Dustin21/interrogator-hardware/contract/io_map.md

# IO map — generated from the pinned USR snapshot

Contract pin: `881fbc1ba3e9c62c94d481077ae7dd061a07874b` · sensors: 16 · electrical facets still pending sign-off (USR-3): **16**

> Generated file — do not edit. Regenerate with `python3 contract/scripts/ingest.py`.

| sensor_type | part | vendor | wire_token | class | bus | i2c addrs | logic V | elec status | datasheet rev |
|---|---|---|---|---|---|---|---|---|---|
| ADS1115 | ADS1115 | Texas Instruments | ADS1115 | adc | i2c | — | 3.3 | ⚠ pending | TODO |
| AMG8833 | AMG8833 (Grid-EYE) | Panasonic | AMG8833 | thermal_imager | i2c | — | 3.3 | ⚠ pending | TODO |
| AS7263 | AS7263 | ams OSRAM | AS7263 | spectral_nir | i2c | — | 3.3 | ⚠ pending | TODO |
| AS7331 | AS7331 | ams OSRAM | AS7331 | uv | i2c | — | 3.3 | ⚠ pending | TODO |
| AS7343 | AS7343 | ams OSRAM | AS7343 | spectral_vis | i2c | — | 3.3 | ⚠ pending | TODO |
| BME688 | BME688 | Bosch Sensortec | BME688 | env_gas | i2c | — | 3.3 | ⚠ pending | BST-BME688-DS000-03 Rev 1 |
| BMV080 | BMV080 | Bosch Sensortec | BMV080 | particulate | i2c | — | 3.3 | ⚠ pending | TODO |
| BNO085 | BNO085 | Bosch Sensortec (CEVA/Hillcrest) | BNO085 | imu | i2c | — | 3.3 | ⚠ pending | TODO |
| MAX30102 | MAX30102 | Maxim Integrated (ADI) | MAX30102 | pulse_oximeter | i2c | — | 3.3 | ⚠ pending | TODO |
| MIKROE_4036 | MIKROE-4036 | MikroElektronika | MIKROE_4036 | radiation | digital_pulse | — | 3.3 | ⚠ pending | TODO |
| MPR121 | MPR121 | NXP Semiconductors | MPR121 | capacitive_touch | i2c | — | 3.3 | ⚠ pending | TODO |
| NEO_M9N | NEO-M9N | u-blox | GPS | gnss | i2c | — | 3.3 | ⚠ pending | TODO |
| SGP41 | SGP41 | Sensirion | SGP41 | voc_nox_gas | i2c | — | 3.3 | ⚠ pending | TODO |
| TMAG5273 | TMAG5273 | Texas Instruments | TMAG5273 | magnetometer | i2c | — | 3.3 | ⚠ pending | TODO |
| VL53L8CX | VL53L8CX | STMicroelectronics | VL53L8CX | tof_imager | i2c | — | 3.3 | ⚠ pending | TODO |
| XM125 | XM125 (A121) | Acconeer | XM125 | radar_presence | i2c | — | 3.3 | ⚠ pending | TODO |
