Dustin21/interrogator-hardware/enclosure/bean_iso.png

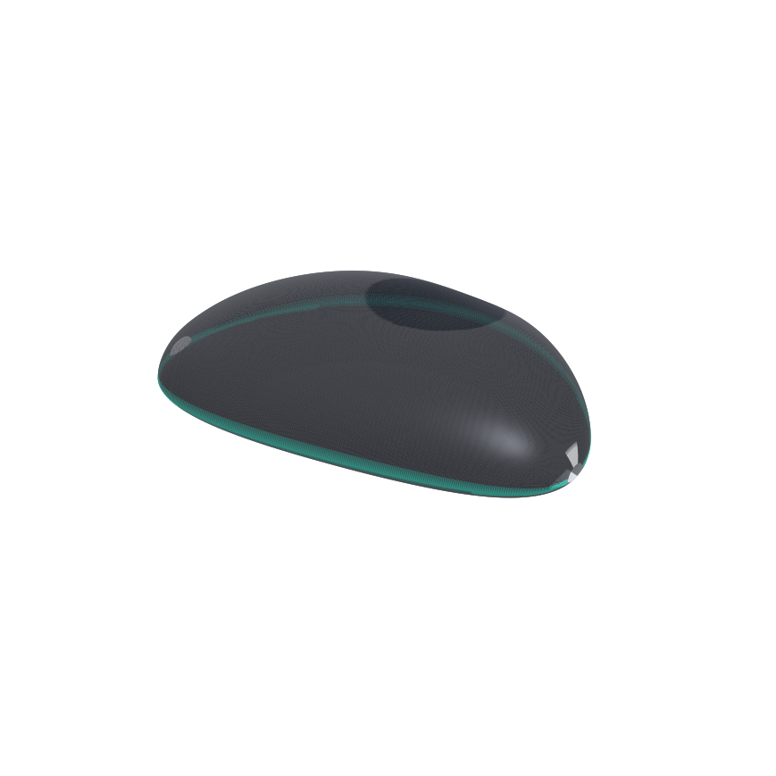
enclosure/bean_iso.png
