Dustin21/interrogator-hardware/enclosure/bean_side.png

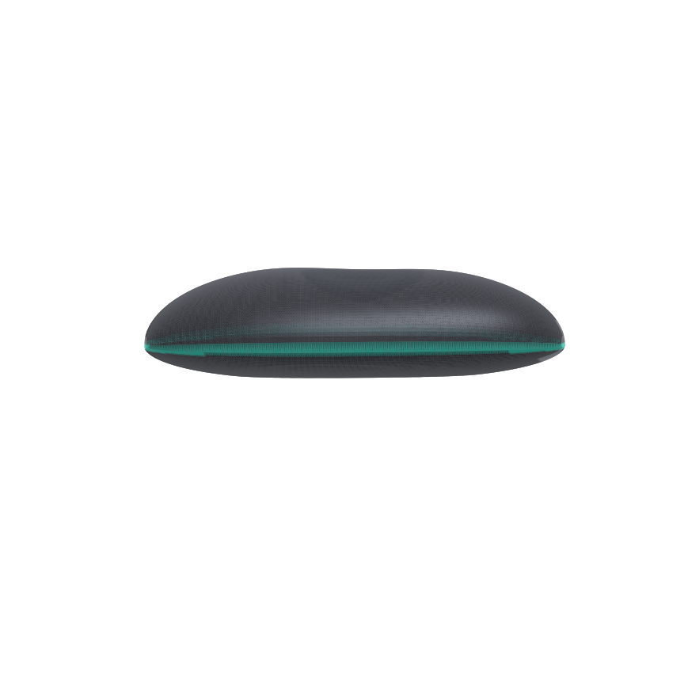
enclosure/bean_side.png
