Dustin21/interrogator-hardware/enclosure/bean_thumb.png

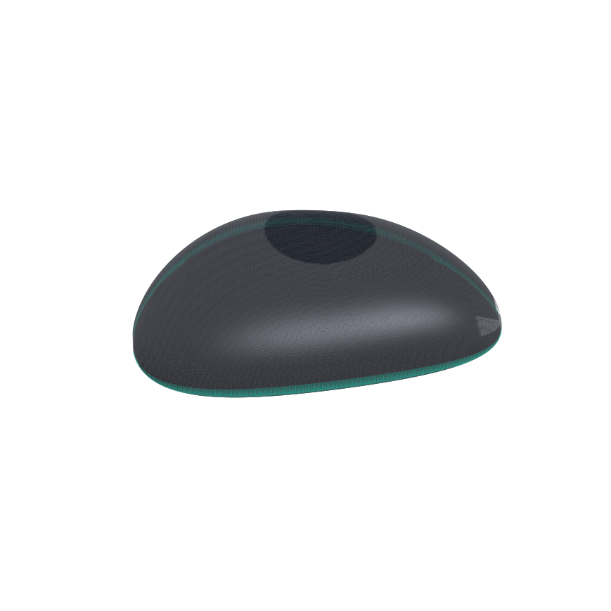
enclosure/bean_thumb.png
