Dustin21/interrogator-hardware/enclosure/bean_top.png

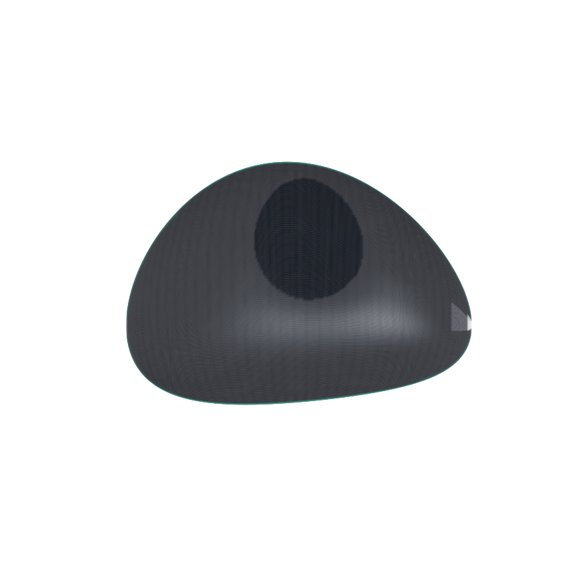
enclosure/bean_top.png
