Dustin21/interrogator-hardware/enclosure/concept_wand_iso.png

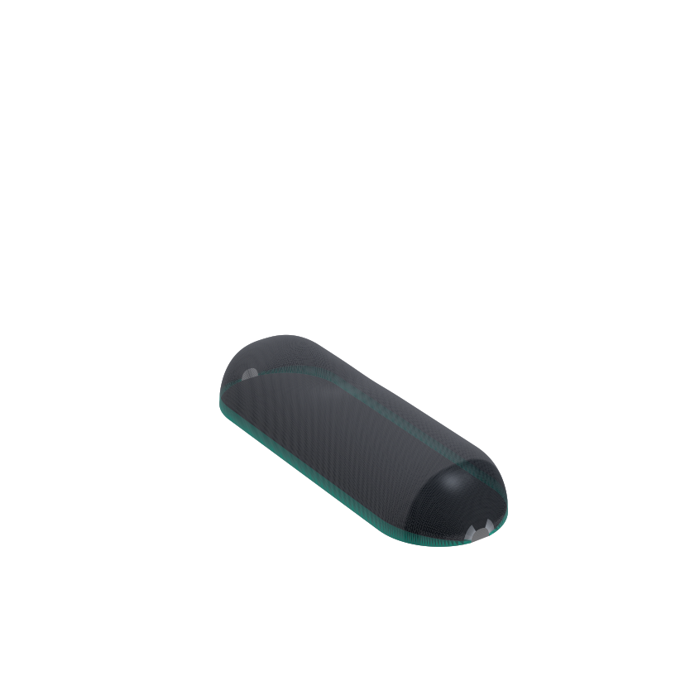
enclosure/concept_wand_iso.png
