Dustin21/interrogator-hardware/enclosure/concept_wand_side.png

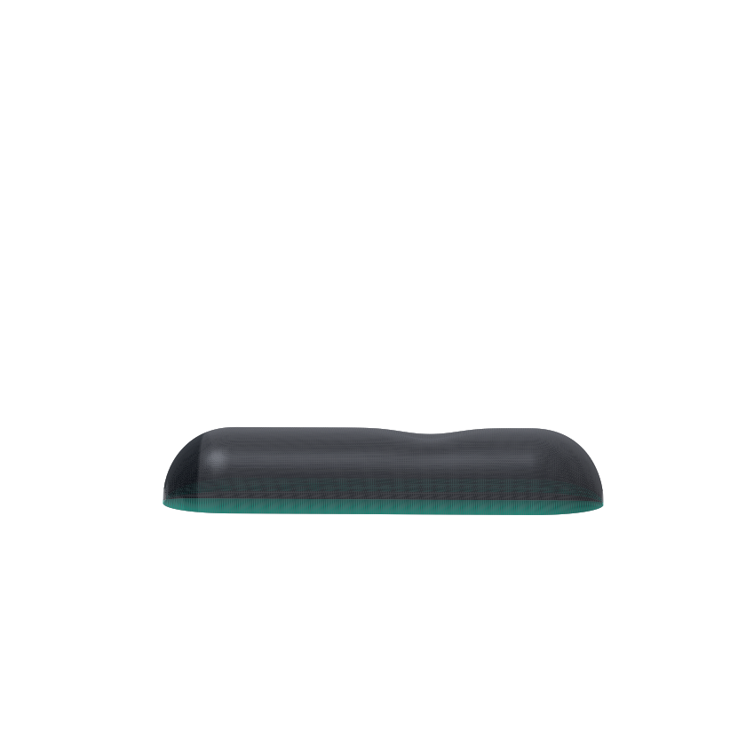
enclosure/concept_wand_side.png
