Dustin21/interrogator-hardware/enclosure/scanner_iso_rear.png

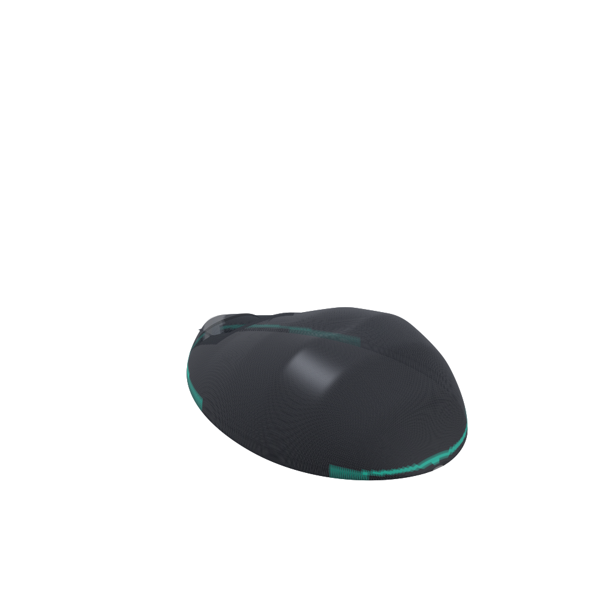
enclosure/scanner_iso_rear.png
