Dustin21/interrogator-hardware/enclosure/scanner_top.png

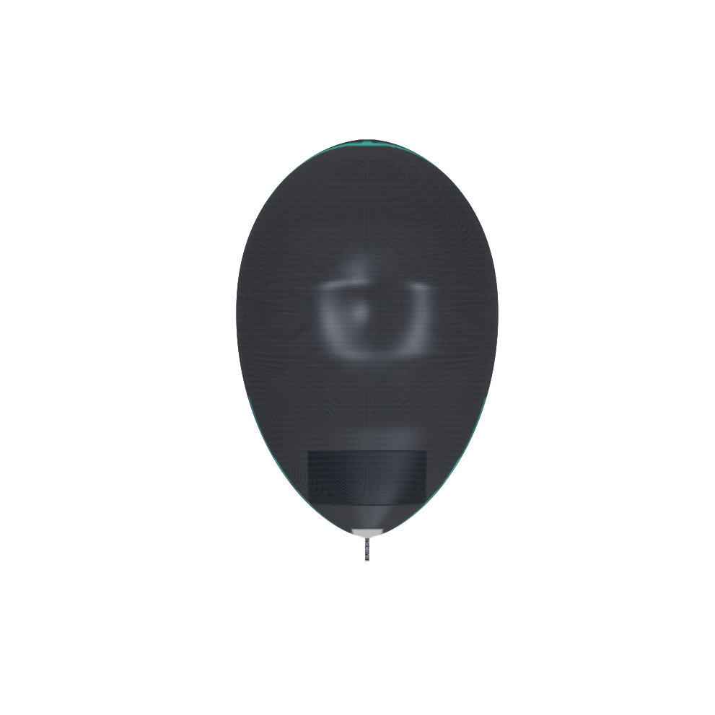
enclosure/scanner_top.png
