Dustin21/interrogator-hardware/enclosure/stone_edge.png

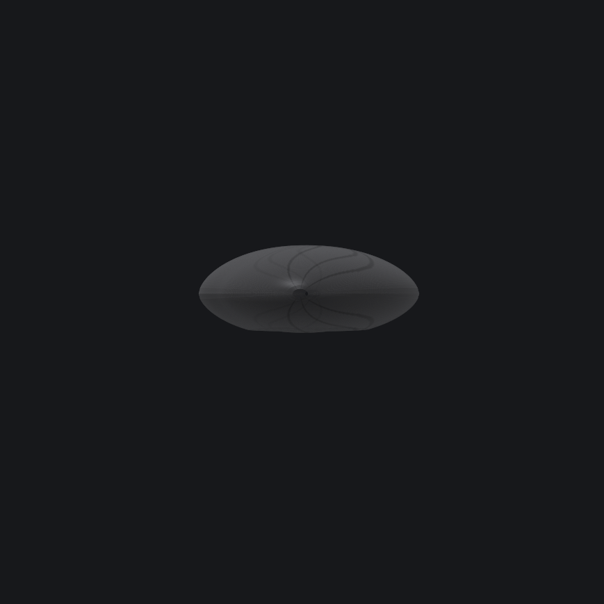
enclosure/stone_edge.png
