Dustin21/interrogator-hardware/enclosure/stone_front.png

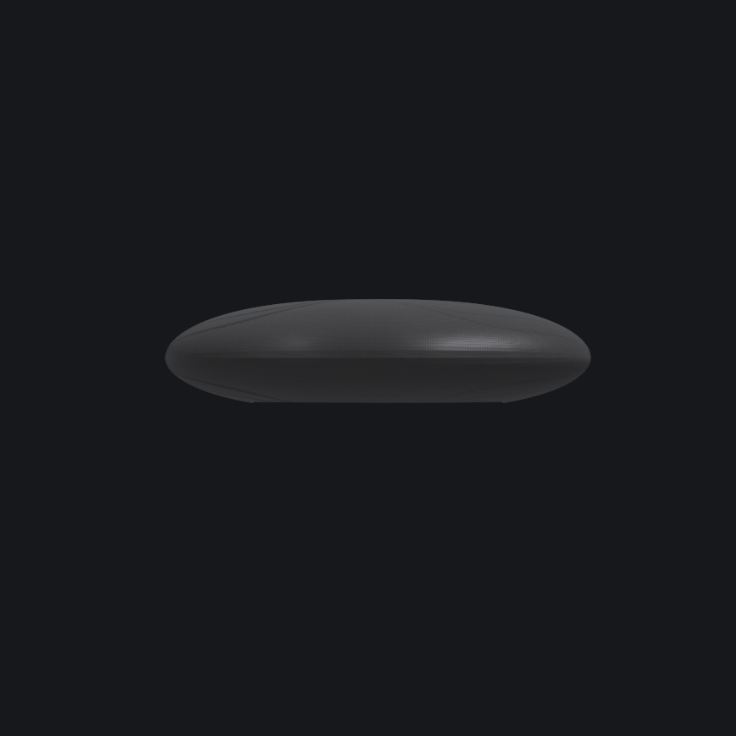
enclosure/stone_front.png
