Dustin21/interrogator-hardware/enclosure/stone_top.png

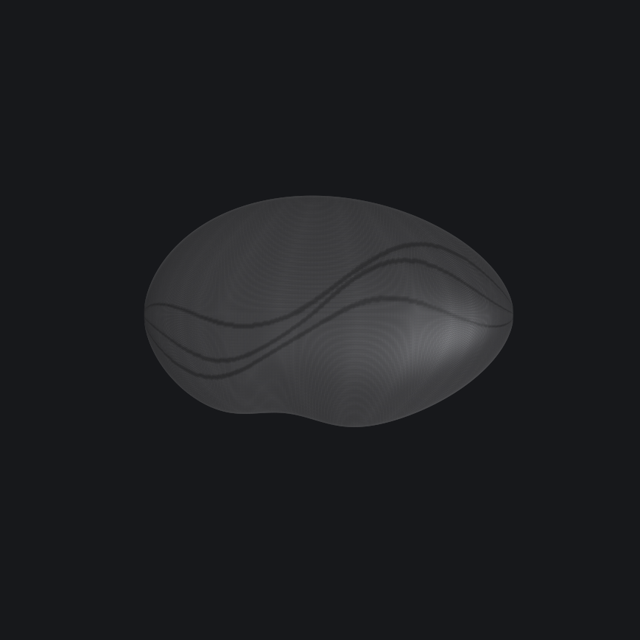
enclosure/stone_top.png
